froks/textclock/software/neopixel.py

# NeoPixel driver for MicroPython
# MIT license; Copyright (c) 2016 Damien P. George, 2021 Jim Mussared

# only included to check api compatibility when debugging/testing on non-target-hw


class NeoPixel:
    # G R B W
    ORDER = (1, 0, 2, 3)

    def __init__(self, pin, n, bpp=3, timing=1):
        self.n = n
        self.bpp = bpp
        self.buf = bytearray(n * bpp)

    def __len__(self):
        return self.n

    def __setitem__(self, i, v):
        offset = i * self.bpp
        for i in range(self.bpp):
            self.buf[offset + self.ORDER[i]] = v[i]

    def __getitem__(self, i):
        offset = i * self.bpp
        return tuple(self.buf[offset + self.ORDER[i]] for i in range(self.bpp))

    def fill(self, v):
        b = self.buf
        l = len(self.buf)
        bpp = self.bpp
        for i in range(bpp):
            c = v[i]
            j = self.ORDER[i]
            while j < l:
                b[j] = c
                j += bpp

    def write(self):
        pass
